FROM-THE-EARTH/canbeta/circuits/images/parent_sch.png

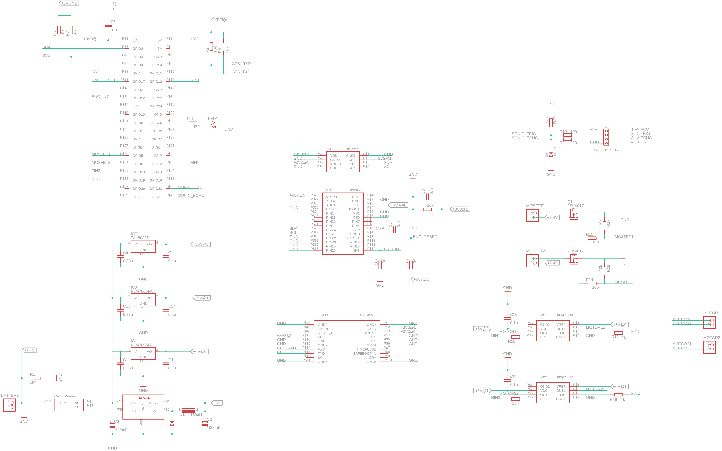
circuits/images/parent_sch.png
