FROM-THE-EARTH/canbeta/circuits/system_block.gif

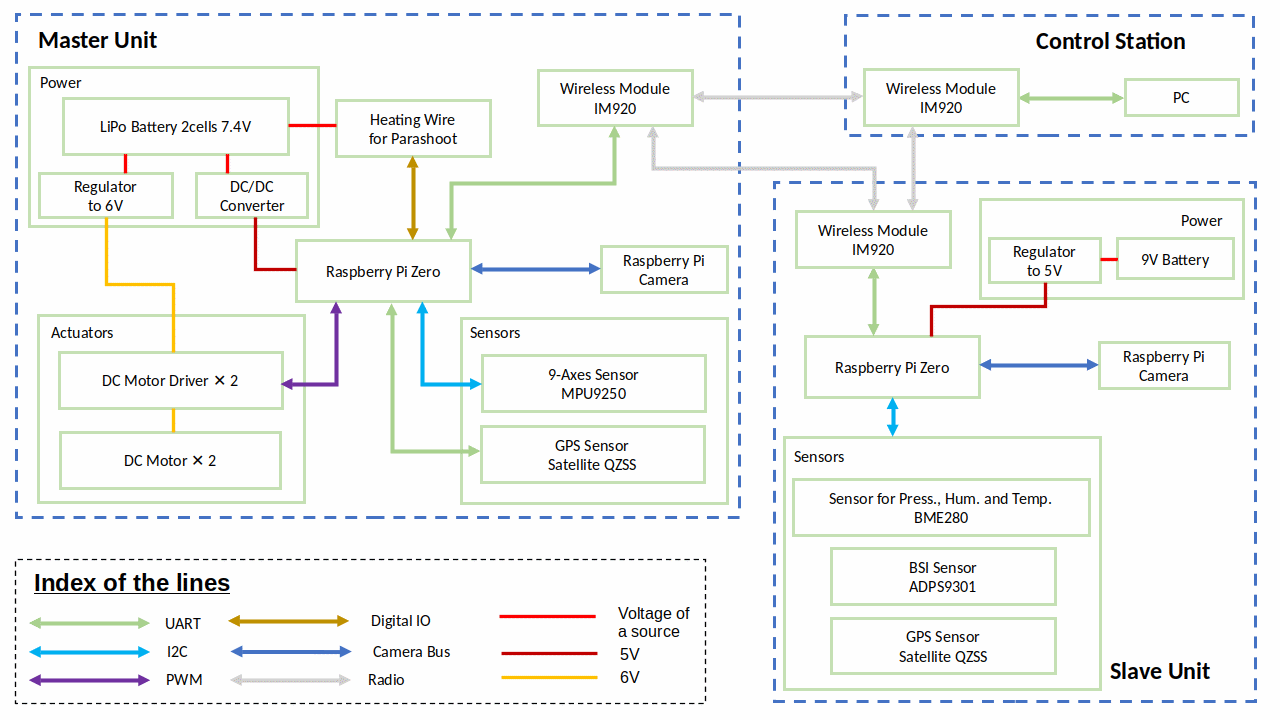
circuits/system_block.gif
