FROM-THE-EARTH/canbeta/data/precursor/acc_x-altitude.png

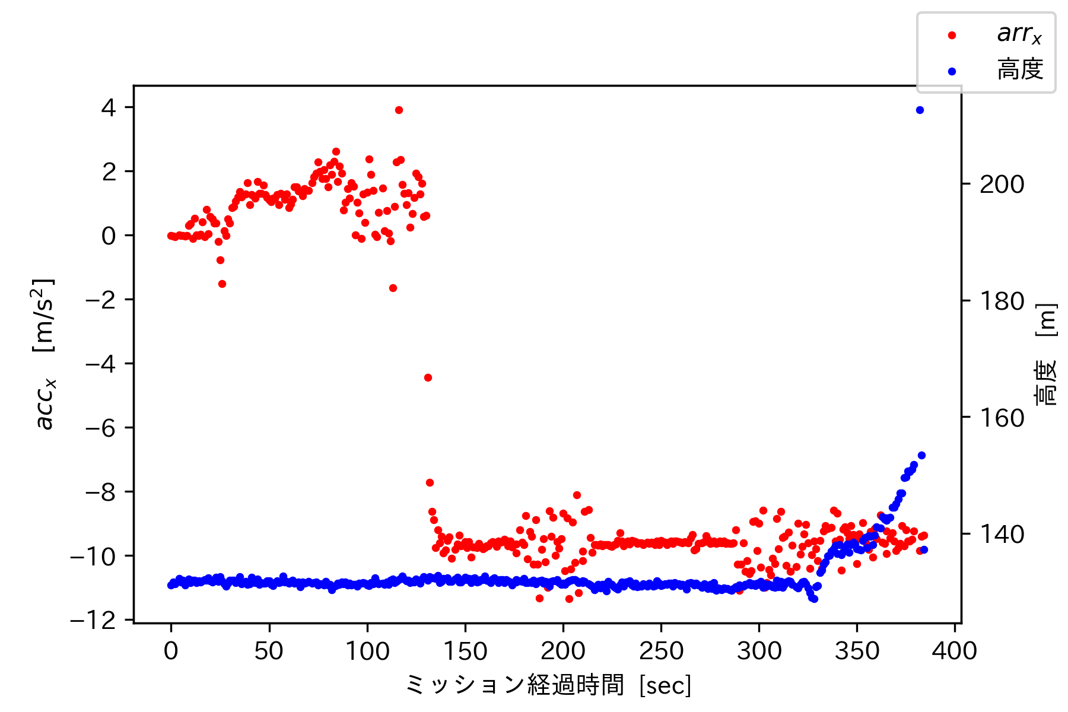
data/precursor/acc_x-altitude.png
