FROM-THE-EARTH/canbeta/data/precursor/acc_xyz.png

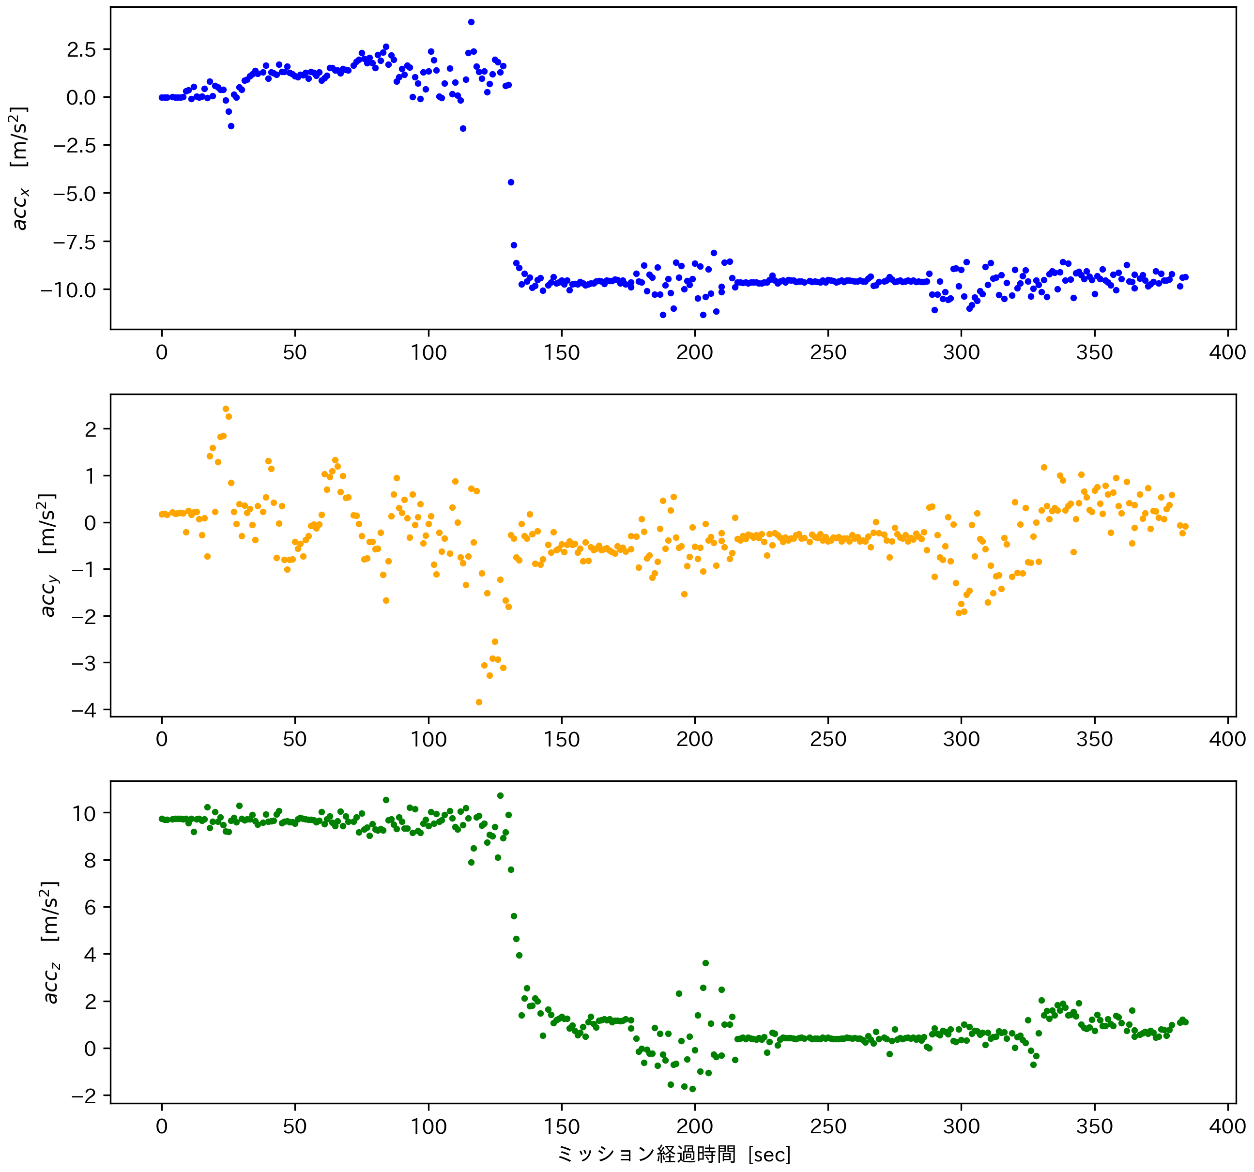
data/precursor/acc_xyz.png
