FROM-THE-EARTH/canbeta/data/precursor/acc_z-altitude.png

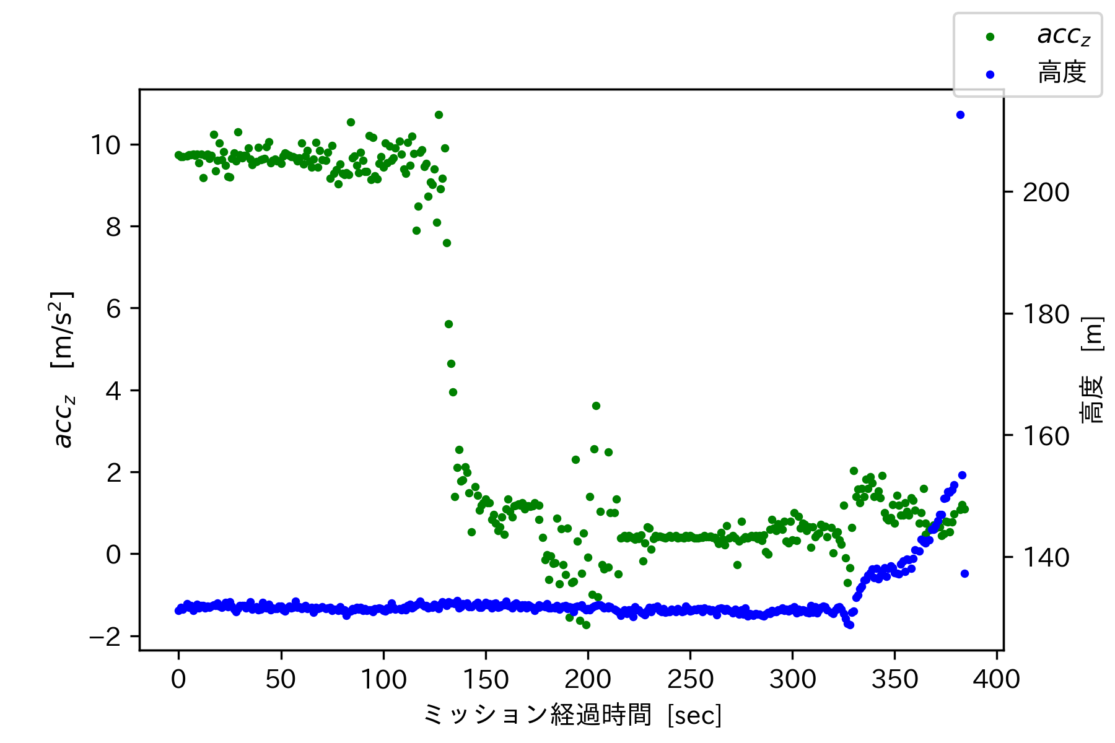
data/precursor/acc_z-altitude.png
