FROM-THE-EARTH/canbeta/data/precursor/gyro_xyz.png

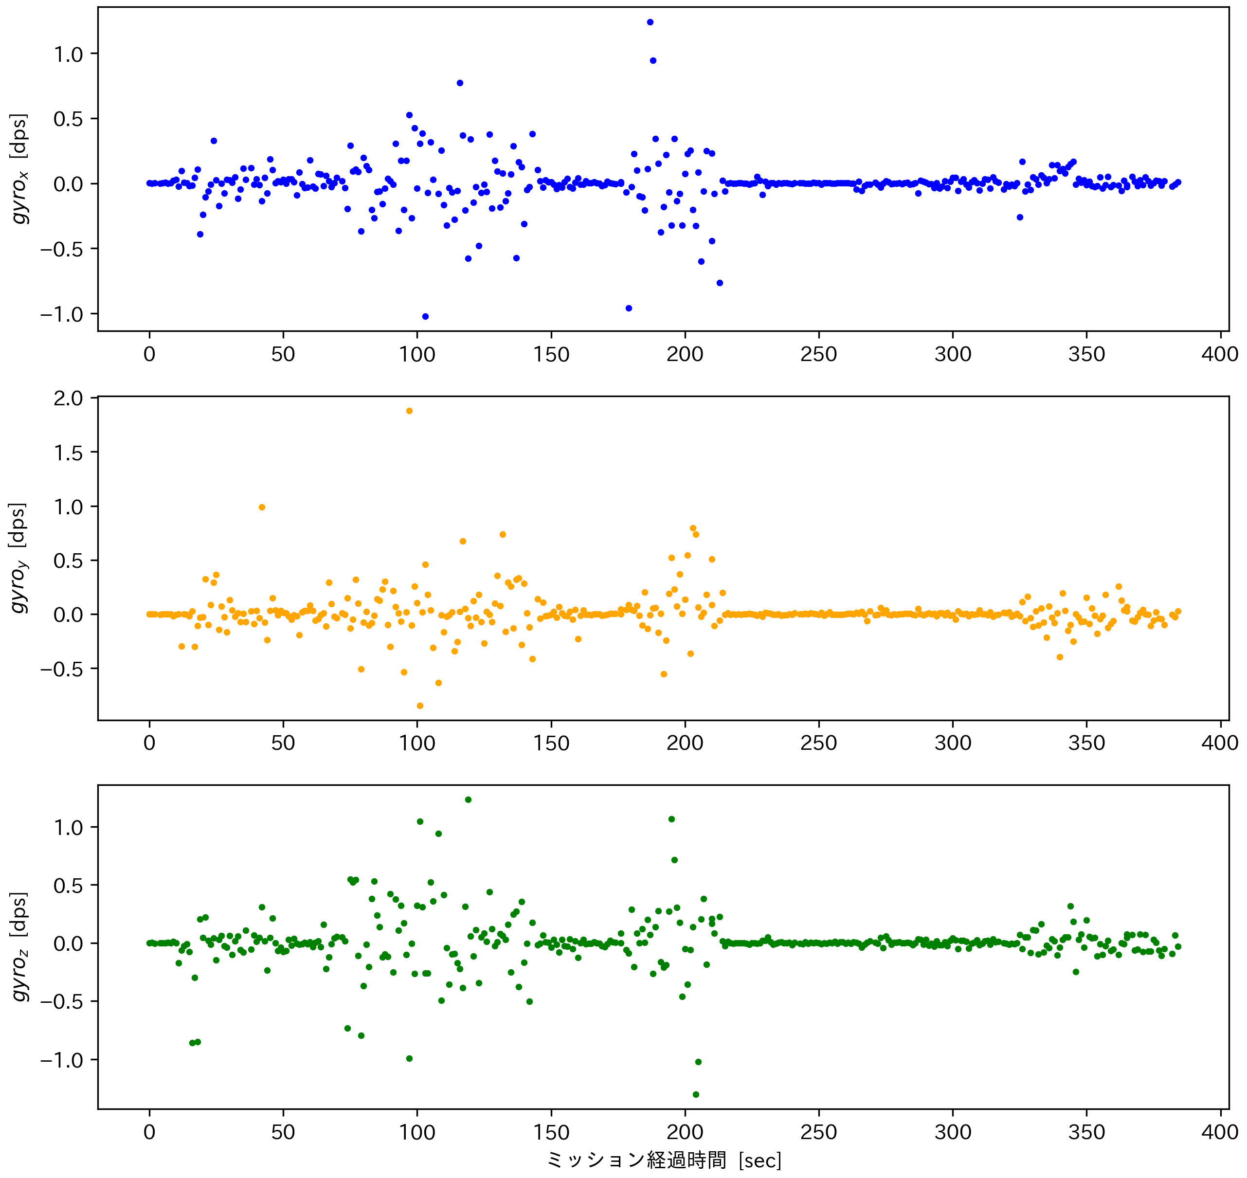
data/precursor/gyro_xyz.png
