FROM-THE-EARTH/canbeta/data/precursor/press-alitude&temp.png

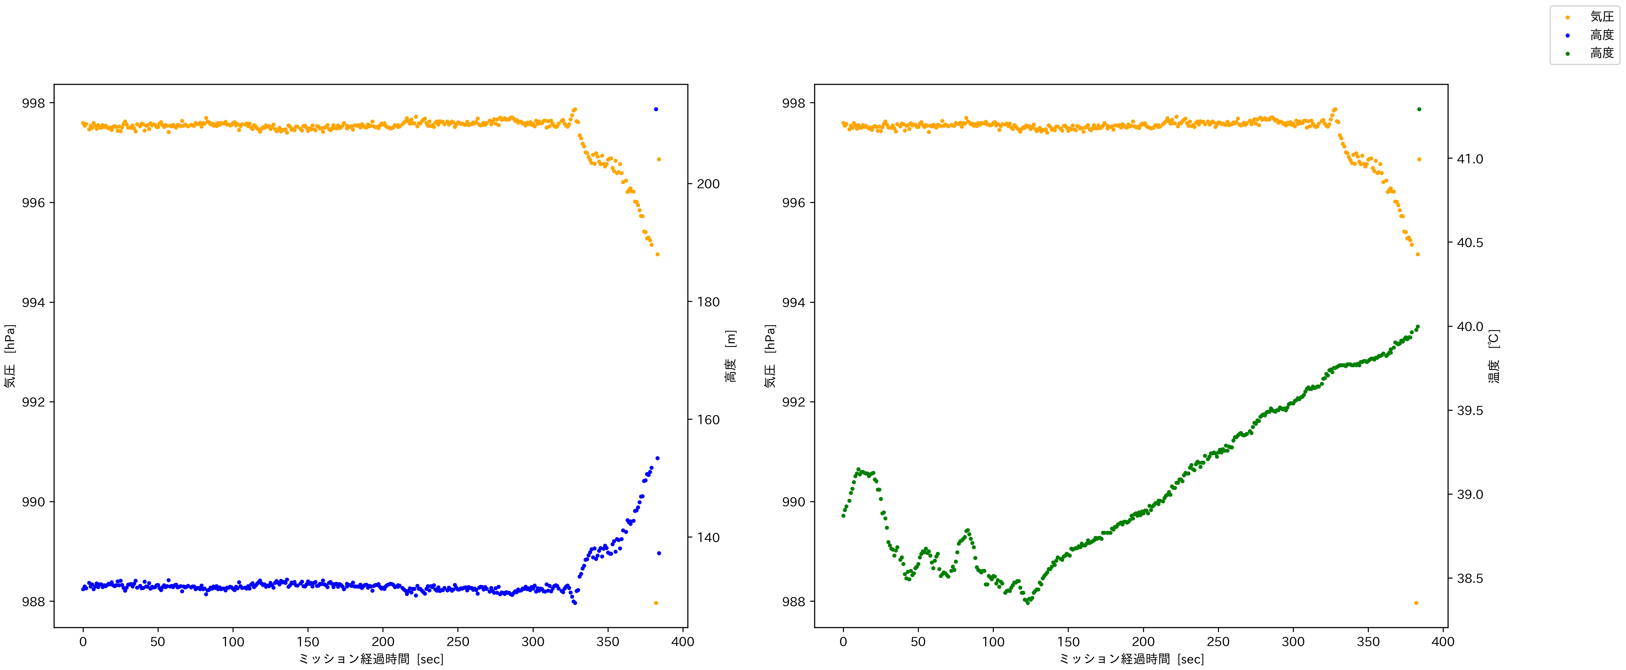
data/precursor/press-alitude&temp.png
