FROM-THE-EARTH/canbeta/data/precursor/press-altitude_more.png

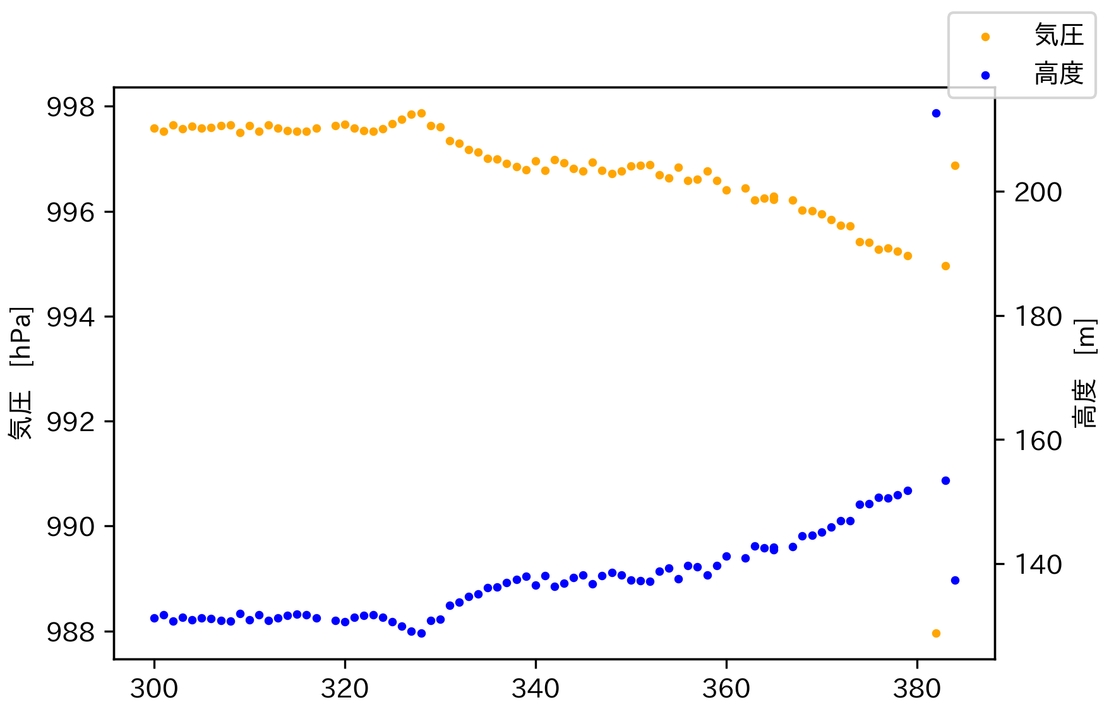
data/precursor/press-altitude_more.png
