FROM-THE-EARTH/canbeta/docs/nodes/parent/img/child_separate_node.png

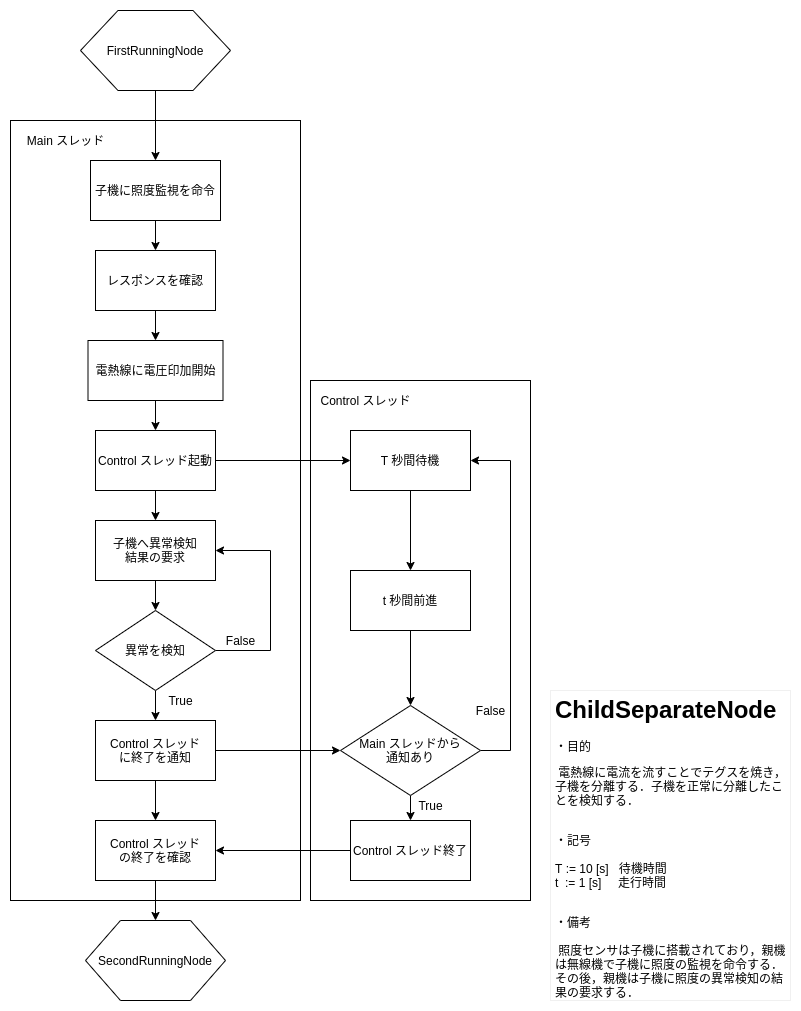
docs/nodes/parent/img/child_separate_node.png
