FROM-THE-EARTH/canbeta/docs/nodes/parent/img/first_running_node.png

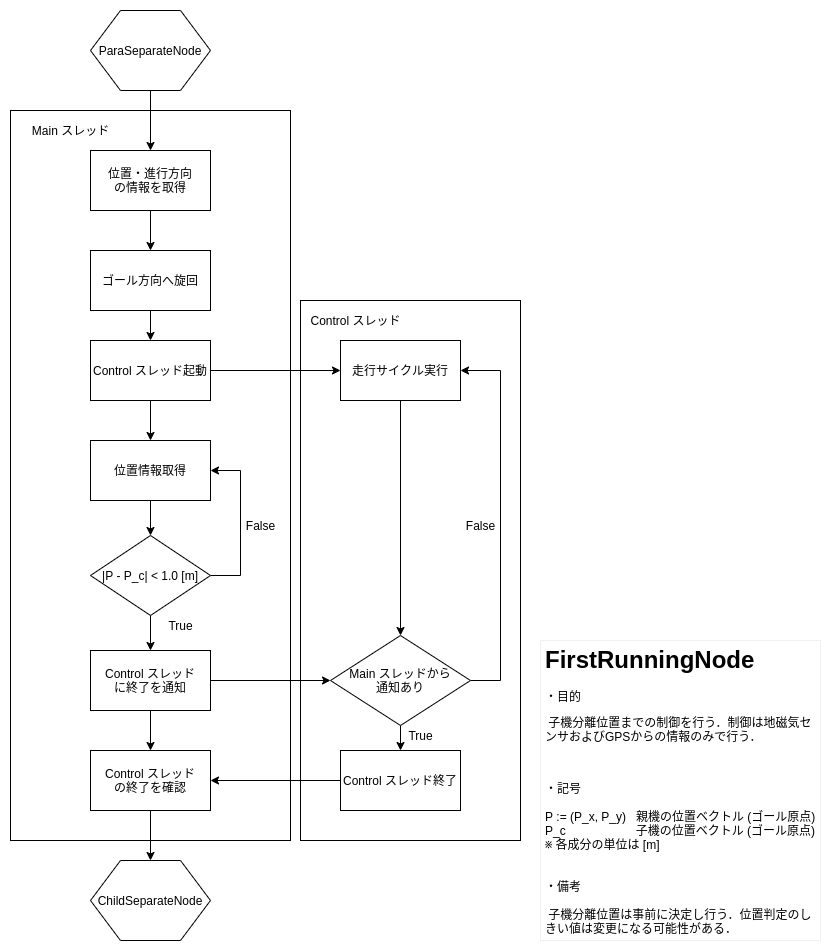
docs/nodes/parent/img/first_running_node.png
