FROM-THE-EARTH/canbeta/docs/nodes/parent/img/para_separate_node.png

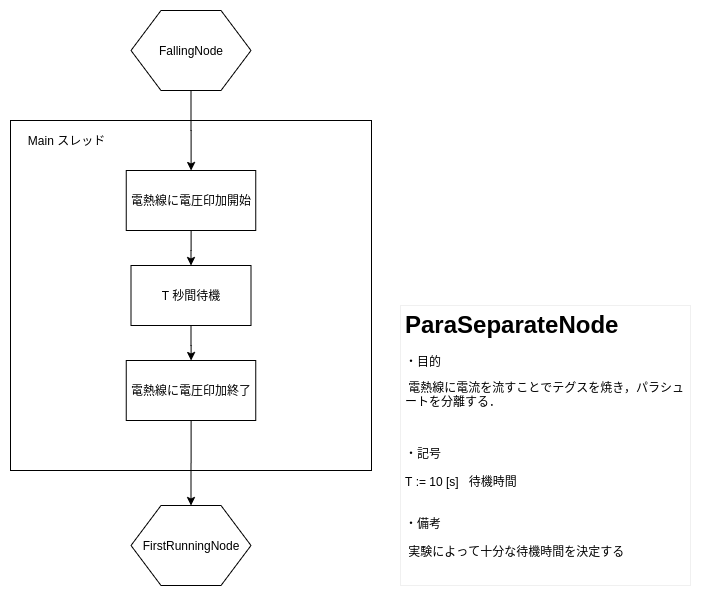
docs/nodes/parent/img/para_separate_node.png
