FROM-THE-EARTH/canbeta/experiments/falling/result/LoggingModel_2020.11.19-17.02.41.csv

sensor_controller-acc_x | sensor_controller-acc_y | sensor_controller-acc_z | sensor_controller-altitude | sensor_controller-altitude_gps | sensor_controller-gra_x | sensor_controller-gra_y | sensor_controller-gra_z | sensor_controller-heading | sensor_controller-latitude | sensor_controller-longitude | sensor_controller-pitch | sensor_controller-press | sensor_controller-roll | sensor_controller-temp
-0.05 | -0.08 | 0.12 | 27.36433916189891 |  | -0.64 | 7.16 | 6.66 | 294.625 |  |  | -3.75 | 1010.0131230163574 | 47.0625 | 18.99599065223936
-0.05 | -0.08 | 0.12 | 27.36433916189891 |  | -0.64 | 7.16 | 6.66 | 294.625 |  |  | -3.75 | 1010.0131230163574 | 47.0625 | 18.99599065223936
-0.05 | -0.08 | 0.12 | 27.36433916189891 |  | -0.64 | 7.16 | 6.66 | 294.625 |  |  | -3.75 | 1010.0131230163574 | 47.0625 | 18.99599065223936
-0.05 | -0.08 | 0.12 | 27.36433916189891 |  | -0.64 | 7.16 | 6.66 | 294.625 |  |  | -3.75 | 1010.0131230163574 | 47.0625 | 18.99599065223936
-0.05 | -0.08 | 0.12 | 27.36433916189891 |  | -0.64 | 7.16 | 6.66 | 294.625 |  |  | -3.75 | 1010.0131230163574 | 47.0625 | 18.99599065223936
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
