FROM-THE-EARTH/canbeta/experiments/falling/exp_falling.py

import pigpio
from pisat.actuator import BD62xx, TwoWheels
from pisat.comm.transceiver import Im920
from pisat.core.cansat import CanSat
from pisat.core.nav import Context
from pisat.core.manager import ComponentManager
from pisat.core.logger import (
    DataLogger, SensorController, LogQueue, SystemLogger
)
from pisat.handler import (
    PigpioI2CHandler, PyserialSerialHandler,
    PigpioDigitalInputHandler, PigpioDigitalOutputHandler
)
from pisat.handler.pigpio_pwm_handler import PigpioPWMHandler
from pisat.sensor import Bno055, Bme280, SamM8Q, HcSr04

from can09.parent.model import LoggingModel
from can09.parent.nodes import *
import can09.parent.setting as setting


# NOTE For test
setting.ALTITUDE_GROUND = 20                    # [m]
FallingNode.THRESHOLD_RISING_DETECT = 5        # [m]
FallingNode.THRESHOLD_LANDING_DETECT = 2        # [m]


def main():

    # device setting
    pi = pigpio.pi()
    
    handler_bno055 = PigpioI2CHandler(pi, setting.I2C_ADDRESS_BNO055)
    handler_bme280 = PigpioI2CHandler(pi, setting.I2C_ADDRESS_BME280)
    handler_gps = PyserialSerialHandler(setting.SERIAL_PORT_GPS)
    # handler_im920 = PyserialSerialHandler(setting.SERIAL_PORT_IM920)
    
    handler_motor_L_fin = PigpioPWMHandler(pi, setting.GPIO_MOTOR_L_FIN, setting.MOTOR_PWM_FREQ)
    handler_motor_L_rin = PigpioPWMHandler(pi, setting.GPIO_MOTOR_L_RIN, setting.MOTOR_PWM_FREQ)
    handler_motor_R_fin = PigpioPWMHandler(pi, setting.GPIO_MOTOR_R_FIN, setting.MOTOR_PWM_FREQ)
    handler_motor_R_rin = PigpioPWMHandler(pi, setting.GPIO_MOTOR_R_RIN, setting.MOTOR_PWM_FREQ)
    handler_mosfet_para = PigpioDigitalOutputHandler(pi, setting.GPIO_MOSFET_PARA, name=setting.NAME_MOSFET_PARA)
    handler_mosfet_child = PigpioDigitalOutputHandler(pi, setting.GPIO_MOSFET_CHILD, name=setting.NAME_MOSFET_CHILD)
    handler_sonic_trig = PigpioDigitalOutputHandler(pi, setting.GPIO_SONIC_TRIG)
    handler_sonic_echo = PigpioDigitalInputHandler(pi, setting.GPIO_SONIC_ECHO)
    handler_led = PigpioDigitalOutputHandler(pi, setting.GPIO_LED, name=setting.NAME_LED)

    # actuator
    motor_L = BD62xx(handler_motor_L_fin, handler_motor_L_rin, name=setting.NAME_MOTOR_L)
    motor_R = BD62xx(handler_motor_R_fin, handler_motor_R_rin, name=setting.NAME_MOTOR_R)
    wheels = TwoWheels(motor_L, motor_R, name=setting.NAME_WHEELS)

    # transceiver
    # im920 = Im920(handler_im920, name=setting.NAME_IM920)

    # sensor
    bno055 = Bno055(handler_bno055, name=setting.NAME_BNO055)
    bno055.change_operation_mode(Bno055.OperationMode.NDOF)
    bme280 = Bme280(handler_bme280, name=setting.NAME_BME280)
    gps = SamM8Q(handler_gps, name=setting.NAME_GPS)
    sonic = HcSr04(handler_sonic_echo, handler_sonic_trig, name=setting.NAME_SUPERSONIC)
    
    con = SensorController(LoggingModel, bno055, bme280, gps, sonic, name=setting.NAME_SENSOR_CONTROLLER)
    que = LogQueue(LoggingModel, maxlen=1000, name=setting.NAME_LOGQUEUE)
    dlogger = DataLogger(con, que, name=setting.NAME_DATA_LOGGER)

    slogger = SystemLogger(name=setting.NAME_SYSTEM_LOGGER)
    slogger.setFileHandler()

    # register callable components in Nodes
    manager = ComponentManager(motor_L, motor_R, wheels, handler_mosfet_para,
                               handler_mosfet_child, handler_led, dlogger, slogger, 
                               recursive=True, name=setting.NAME_MANAGER)

    # context setting
    context = Context({
                        FallingNode:        {True: ParaSeparateNode,    False: FallingNode},
                        ParaSeparateNode:   {True: None,    False: ParaSeparateNode},
                        },
                    start=FallingNode)

    # build a cansat
    cansat = CanSat(context, manager, dlogger=dlogger, slogger=slogger)
    cansat.run()


if __name__ == "__main__":
    main()
